MUNAKATA-EPC/Artemis_2025/Common_Data/artemis_pic/artemis_text_colored_white_shined.png

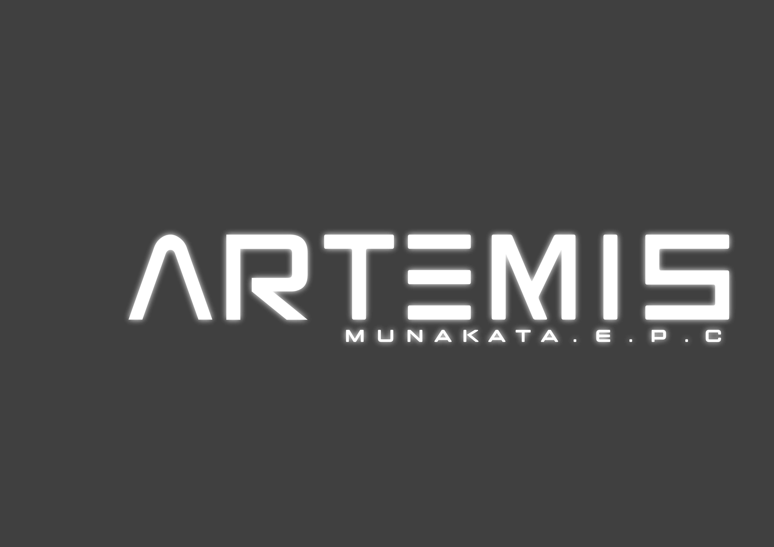
Common_Data/artemis_pic/artemis_text_colored_white_shined.png
