MUNAKATA-EPC/Artemis_2025/Common_Data/artemis_pic/artemis_white.png

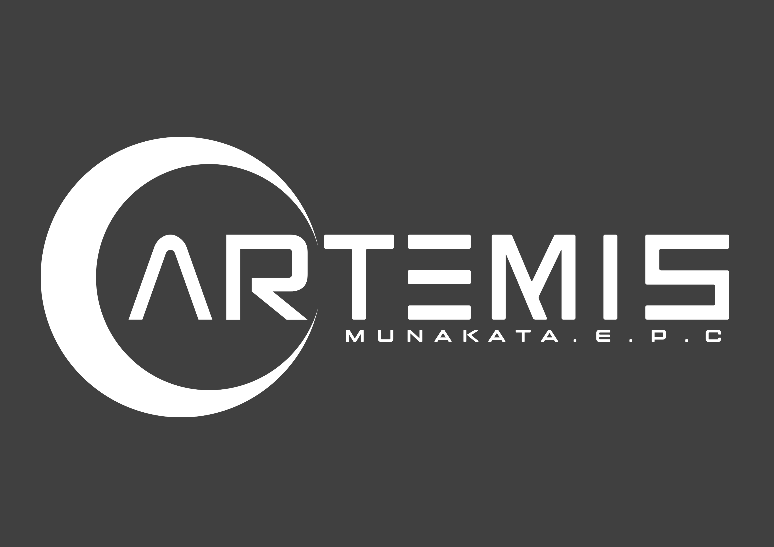
Common_Data/artemis_pic/artemis_white.png
