MUNAKATA-EPC/Artemis_2025/Project_Tsukuyomi (JapanOpen)/Hardware/STEP/VoltageBooster.step

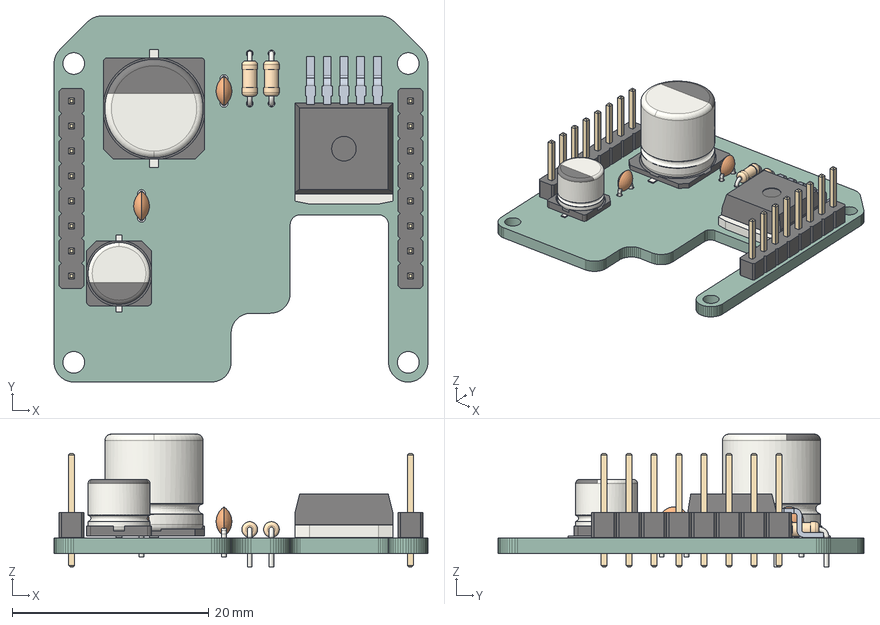
[picture p53: CAD file, 2025-01-11]
Project_Tsukuyomi (JapanOpen)/Hardware/STEP/VoltageBooster.step
38.0 x 37.2 x 13.5 mm
CP_Elec_63x59
R_Axial_DIN0204_L36mm_D16mm_P508mm_Horizontal x 2
CP_Elec_10x105
CQ assembly
PinHeader_1x08_P254mm_Vertical x 2
C_Disc_D30mm_W16mm_P250mm x 2
VoltageBooster PCB
