MUNAKATA-EPC/Artemis_2025/Project_Tsukuyomi (JapanOpen)/Hardware/JLCPCB/Printer/rim.stl

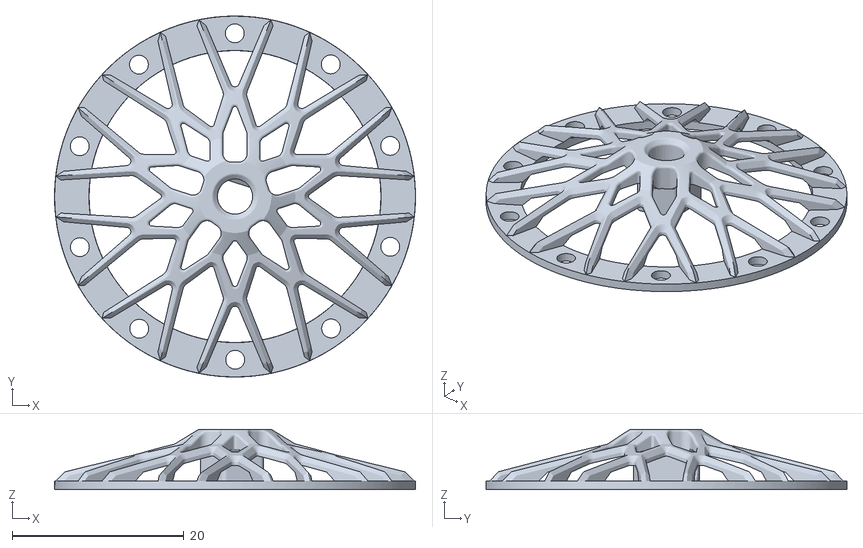
[picture p54: CAD file, 2025-01-11]
Project_Tsukuyomi (JapanOpen)/Hardware/JLCPCB/Printer/rim.stl
42.0 x 42.0 x 7.00
