MUNAKATA-EPC/Artemis_2025/Project_Tsukuyomi (JapanOpen)/Hardware/JLCPCB/Printer/motormount2-1.stl

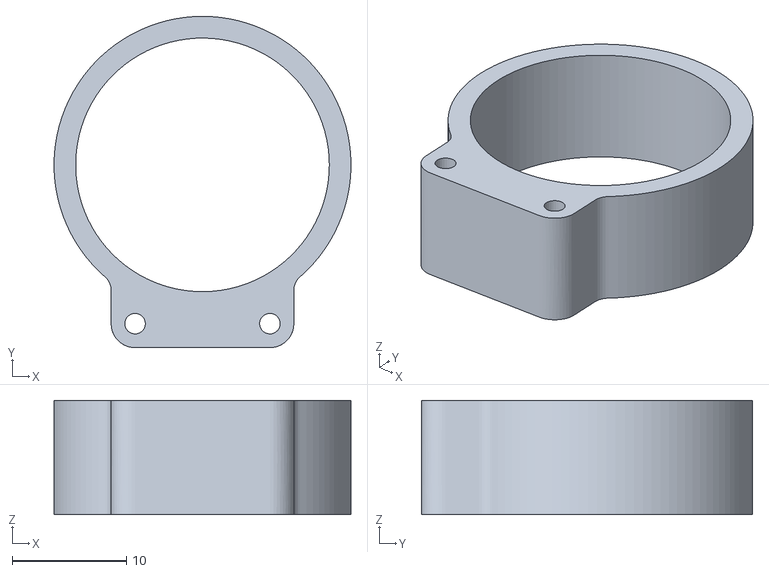
[picture p55: CAD file, 2025-01-11]
Project_Tsukuyomi (JapanOpen)/Hardware/JLCPCB/Printer/motormount2-1.stl
26.0 x 29.0 x 10.0
