MUNAKATA-EPC/Artemis_2025/Project_Tsukuyomi (JapanOpen)/Hardware/JLCPCB/Printer/handle.stl

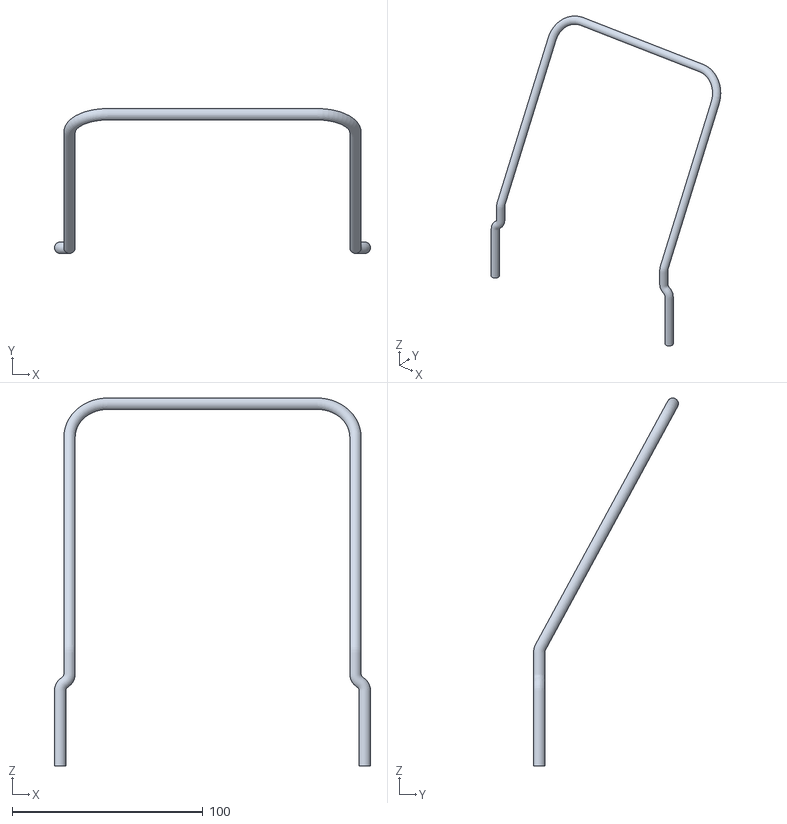
[picture p56: CAD file, 2025-01-11]
Project_Tsukuyomi (JapanOpen)/Hardware/JLCPCB/Printer/handle.stl
165.8 x 76.0 x 193.0
