MUNAKATA-EPC/Artemis_2025/Common_Data/Tournaments_Data/2025_02_JapanOpen/PresentationSheet/SWO008_Munako Artemis_九州.pdf

## 福岡県立宗像高等学校

# チームメンバー

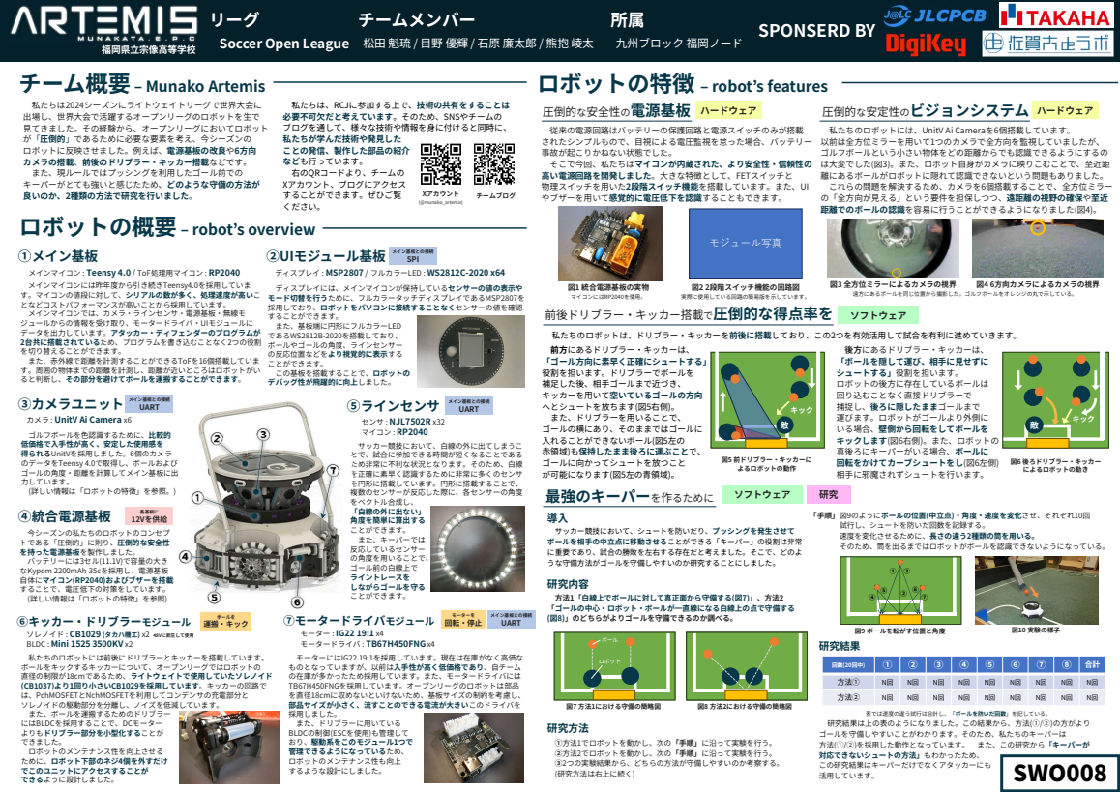
[picture p57: page 1]
研究結果; 九州ブロック 福岡ノード; 前後ドリブラー・キッカー搭載で圧倒的な得点率を; (図8)」のどちらがよりゴールを守備できるのか調べる。; チーム概要‒ Munako Artemis; ロボットの特徴 ‒ robot’s features; 低価格で入手性が高く、安定した使用感を 得られるUnitVを採用しました。6個のカメラ のデータをTeensy 4.0で取得し、ボールおよび ゴールの角度・距離を計算してメイン基板に出 力しています。; UART; 図3 全方位ミラーによるカメラの視界; 図4 6方向カメラによるカメラの視界; 遠方にあるボールを同じ位置から撮影した。ゴルフボールをオレンジの丸で示している。; ➃統合電源基板; 各基板に 12Vを供給; ソフトウェア; ➅キッカー・ドリブラーモジュール; ボールを; 運搬・キック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

SPONSERD BY リーグ
Soccer Open League

松田 魁琉 / 目野 優輝 / 石原 廉太郎 / 熊抱 崚太

私たちは2024シーズンにライトウェイトリーグで世界大会に
出場し、世界大会で活躍するオープンリーグのロボットを生で
見てきました。その経験から、オープンリーグにおいてロボット
が「圧倒的」であるために必要な要素を考え、今シーズンの
ロボットに反映させました。例えば、電源基板の改良や6方向
カメラの搭載、前後のドリブラー・キッカー搭載などです。
また、現ルールではプッシングを利用したゴール前での
キーパーがとても強いと感じたため、どのような守備の方法が
良いのか、2種類の方法で研究を行いました。
ロボットの概要 ‒ robot’s overview
➀メイン基板

ハードウェア 私たちは、RCJに参加する上で、技術の共有をすることは
必要不可欠だと考えています。そのため、SNSやチームの
ブログを通して、様々な技術や情報を身に付けると同時に、
私たちが学んだ技術や発見した
ことの発信、製作した部品の紹介
なども行っています。
右のQRコードより、チームの
Xアカウント、ブログにアクセス
することができます。ぜひご覧
ください。

従来の電源回路はバッテリーの保護回路と電源スイッチのみが搭載
されたシンプルもので、目視による電圧監視を怠った場合、バッテリー
事故が起こりかねない状態でした。
そこで今回、私たちはマイコンが内蔵された、より安全性・信頼性の
高い電源回路を開発しました。大きな特徴として、FETスイッチと
物理スイッチを用いた2段階スイッチ機能を搭載しています。また、UI
やブザーを用いて感覚的に電圧低下を認識することもできます。

私たちのロボットには、UnitV Ai Cameraを6個搭載しています。
以前は全方位ミラーを用いて1つのカメラで全方向を監視していましたが、
ゴルフボールという小さい物体をどの距離からでも認識できるようにするの
は大変でした(図3)。また、ロボット自身がカメラに映りこむことで、至近距
離にあるボールがロボットに隠れて認識できないという問題もありました。
これらの問題を解決するため、カメラを6個搭載することで、全方位ミラー
の「全方向が見える」という要件を担保しつつ、遠距離の視野の確保や至近
距離でのボールの認識を容易に行うことができるようになりました(図4)。

➁UIモジュール基板 メイン基板との接続
SPI ディスプレイ : MSP2807 / フルカラーLED : WS2812C-2020 x64

メインマイコン : Teensy 4.0 / ToF処理用マイコン : RP2040
メインマイコンには昨年度から引き続きTeensy4.0を採用していま
す。マイコンの値段に対して、シリアルの数が多く、処理速度が高いこ
となどコストパフォーマンスが高いことから採用しています。
メインマイコンでは、カメラ・ラインセンサ・電源基板・無線モ
ジュールからの情報を受け取り、モータードライバ・UIモジュールに
データを出力しています。アタッカー・ディフェンダーのプログラムが
2台共に搭載されているため、プログラムを書き込むことなく2つの役割
を切り替えることができます。
また、赤外線で距離を計測することができるToFを16個搭載していま
す。周囲の物体までの距離を計測し、距離が近いところはロボットがい
ると判断し、その部分を避けてボールを運搬することができます。
➂カメラユニット
(詳しい情報は「ロボットの特徴」を参照。) メイン基板との接続
カメラ : UnitV Ai Camera x6 ゴルフボールを色認識するために、比較的

私たちのロボットは、ドリブラー・キッカーを前後に搭載しており、この2つを有効活用して試合を有利に進めていきます。
前方にあるドリブラー・キッカーは、
「ゴール方向に素早く正確にシュートする」
役割を担います。ドリブラーでボールを
補足した後、相手ゴールまで近づき、
キッカーを用いて空いているゴールの方向
へとシュートを放ちます(図5右側)。
また、ドリブラーを用いることで、
ゴールの横にあり、そのままではゴールに
入れることができないボール(図5左の
赤領域)も保持したまま後ろに運ぶことで、
ゴールに向かってシュートを放つこと
が可能になります(図5左の青領域)。
最強のキーパーを作るために
サッカー競技において、シュートを防いだり、プッシングを発生させて
ボールを相手の中立点に移動させることができる「キーパー」の役割は非常
に重要であり、試合の勝敗を左右する存在だと考えました。そこで、どのよ
うな守備方法がゴールを守備しやすいのか研究することにしました。
研究内容
方法1「白線上でボールに対して真正面から守備する(図7)」、方法2 「ゴールの中心・ロボット・ボールが一直線になる白線上の点で守備する

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

➄ラインセンサ メイン基板との接続
UART センサ : NJL7502R x32 マイコン : RP2040

「手順」図9のようにボールの位置(中立点)・角度・速度を変化させ、それぞれ10回
試行し、シュートを防いだ回数を記録する。
速度を変化させるために、⾧さの違う2種類の筒を用いる。
そのため、筒を出るまではロボットがボールを認識できないようになっている。

今シーズンの私たちのロボットのコンセプ
トである「圧倒的」に則り、圧倒的な安全性
を持った電源基板を製作しました。
バッテリーには3セル(11.1V)で容量の大き
なKypom 2200mAh 35cを採用し、電源基板
自体にマイコン(RP2040)およびブザーを搭載
することで、電圧低下の対策をしています。
(詳しい情報は「ロボットの特徴」を参照)

UART モーター : IG22 19:1 x4 モータードライバ : TB67H450FNG x4 モーターにはIG22 19:1を採用しています。現在は在庫がなく高価な

ソレノイド : CB1029 (タカハ機工) x2 48Vに昇圧して使用
BLDC : Mini 1525 3500KV x2 私たちのロボットには前後にドリブラーとキッカーを搭載しています。

ものとなっていますが、以前は入手性が高く低価格であり、自チーム
の在庫が多かったため採用しています。また、モータードライバには
TB67H450FNGを採用しています。オープンリーグのロボットは部品
を直径18cmに収めないといけないため、基板サイズの制約を考慮し、
部品サイズが小さく、流すことのできる電流が大きいこのドライバを
採用しました。
また、ドリブラーに用いている
BLDCの制御(ESCを使用)も管理して
おり、駆動系をこのモジュール1つで
管理できるようになっているため、
ロボットのメンテナンス性も向上
するような設計にしました。

方法➀ | N回 | N回 | N回 | N回 | N回 | N回 | N回 | N回 | N回
方法➁ | N回 | N回 | N回 | N回 | N回 | N回 | N回 | N回 | N回

研究方法
➀方法1でロボットを動かし、次の「手順」に沿って実験を行う。
➁方法2でロボットを動かし、次の「手順」に沿って実験を行う。
➂2つの実験結果から、どちらの方法が守備しやすいのか考察する。
(研究方法は右上に続く)

研究結果は上の表のようになりました。この結果から、方法(➀/➁)の方がより
ゴールを守備しやすいことがわかります。そのため、私たちのキーパーは
方法(➀/➁)を採用した動作となっています。 また、この研究から「キーパーが
対応できないシュートの方法」もわかったため、
この研究結果はキーパーだけでなくアタッカーにも
活用しています。

表では速度の違う試行は合計し、「ボールを防いだ回数」を記している。
