MUNAKATA-EPC/Artemis_2025/Common_Data/component_test/DRV8332DKD/KiCad_Data/DRV8332_test/DRV8332_test.kicad_sch

## KiCad design Common_Data/component_test/DRV8332DKD/KiCad_Data/DRV8332_test/DRV8332_test.kicad_sch (2024-06-09)

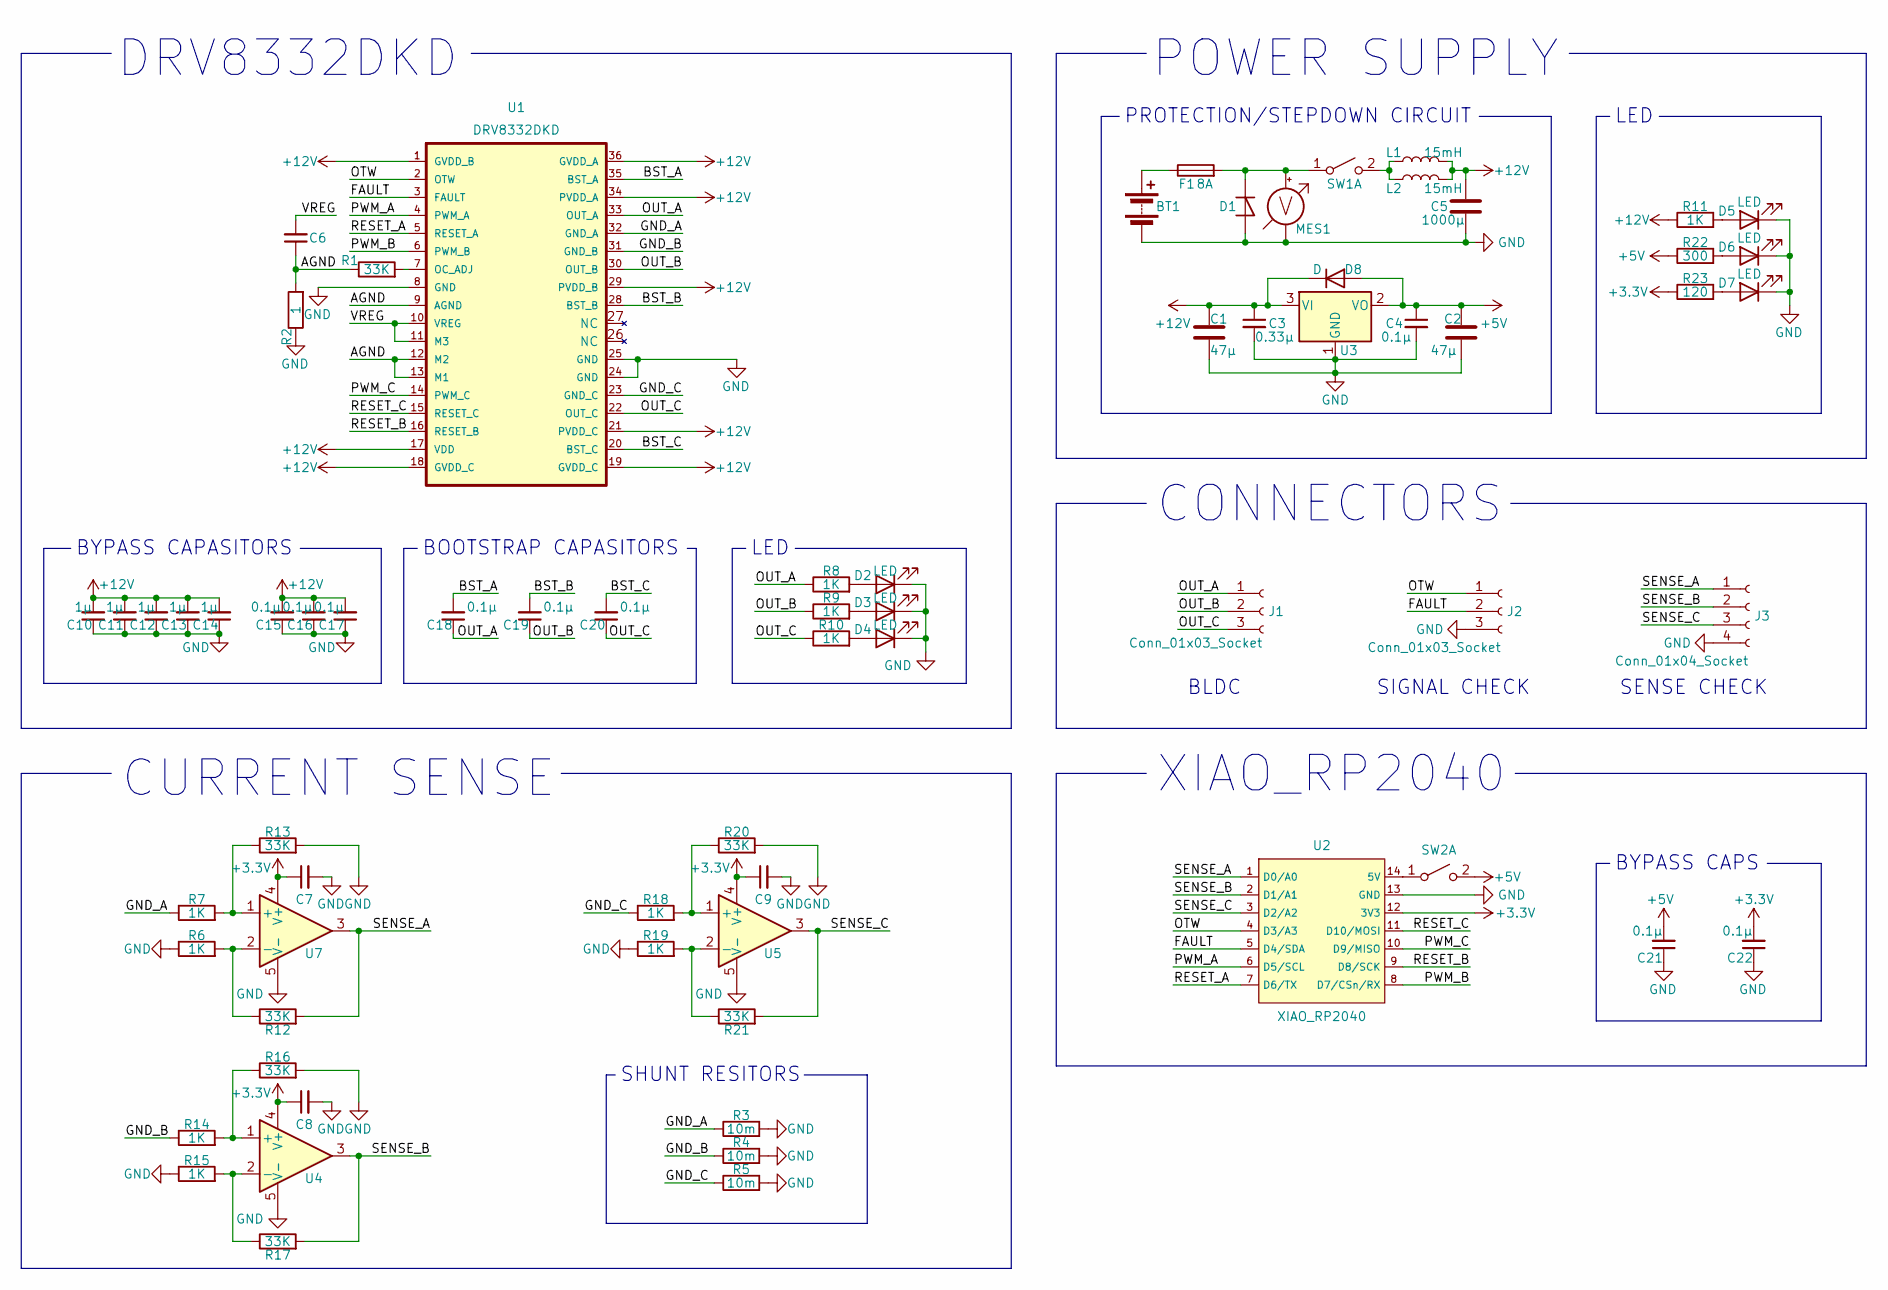
[picture p77: schematic DRV8332_test.kicad_sch]

Parts:
BT1: 11.1v 1300mAh
C1, C2: 47μ
C3: 0.33μ
C4, C15, C16, C17, C18, C19, C20, C21, C22: 0.1μ
C5: 1000μ
C6, C7, C8, C9: C_Small
C10, C11, C12, C13, C14: 1μ
D1: D_Shockley
D2, D3, D4, D5, D6, D7: LED
D8: D
F1: 8A
J1, J2: Conn_01x03_Socket
J3: Conn_01x04_Socket
L1, L2: 15mH
MES1: Voltmeter_DC
R1, R12, R13, R16, R17, R20, R21: 33K
R2: 1
R3, R4, R5: 10m
R6, R7, R8, R9, R10, R11, R14, R15, R18, R19: 1K
R22: 300
R23: 120
SW1, SW2: SW_DPST_x2
U1: DRV8332DKD; SOP65P1420X360-36N
U2: XIAO_RP2040
U3: AZ1117-3.3
U4, U5, U7: type="X" model="OPAMP" lib=""

Connections:
+3.3V: C7.1, C8.1, C9.1, C22.2, R23.1, U2.12 (3V3), U4.4 (V+), U5.4 (V+), U7.4 (V+)
+5V: C2.1, C4.1, C21.2, D8.2 (A), R22.1, SW2.2 (B), U3.2 (VO)
+12V: C1.1, C3.1, C5.1, C10.2, C11.2, C12.2, C13.2, C14.2, C15.2, C16.2, C17.2, D8.1 (K), L1.2, L2.2, R11.1, U1.1 (GVDD_B), U1.17 (VDD), U1.18 (GVDD_C), U1.19 (GVDD_C), U1.21 (PVDD_C), U1.29 (PVDD_B), U1.34 (PVDD_A), U1.36 (GVDD_A), U3.3 (VI)
AGND: C6.1, R1.1, R2.2, U1.9 (AGND), U1.12 (M2), U1.13 (M1)
BST_A: C18.2, U1.35 (BST_A)
BST_B: C19.2, U1.28 (BST_B)
BST_C: C20.2, U1.20 (BST_C)
FAULT: J2.2, U1.3 (FAULT), U2.5 (D4/SDA)
GND: BT1.2 (-), C1.2, C2.2, C3.2, C4.2, C5.2, C7.2, C8.2, C9.2, C10.1, C11.1, C12.1, C13.1, C14.1, C15.1, C16.1, C17.1, C21.1, C22.1, D1.2 (A), D2.1 (K), D3.1 (K), D4.1 (K), D5.1 (K), D6.1 (K), D7.1 (K), J2.3, J3.4, MES1.1 (-), R2.1, R3.2, R4.2, R5.2, R6.1, R13.2, R15.1, R16.2, R19.1, R20.2, U1.8 (GND), U1.24 (GND), U1.25 (GND), U2.13 (GND), U3.1 (GND), U4.5 (V-), U5.5 (V-), U7.5 (V-)
GND_A: R3.1, R7.1, U1.32 (GND_A)
GND_B: R4.1, R14.1, U1.31 (GND_B)
GND_C: R5.1, R18.1, U1.23 (GND_C)
unnamed: BT1.1 (+), F1.1
unnamed: D1.1 (K), F1.2, MES1.2 (+), SW1.1 (A)
unnamed: D2.2 (A), R8.2
unnamed: D3.2 (A), R9.2
unnamed: D4.2 (A), R10.2
unnamed: D5.2 (A), R11.2
unnamed: D6.2 (A), R22.2
unnamed: D7.2 (A), R23.2
unnamed: L1.1, L2.1, SW1.2 (B)
unnamed: R1.2, U1.7 (OC_ADJ)
unnamed: R6.2, R12.1, U7.2 (-)
unnamed: R7.2, R13.1, U7.1 (+)
unnamed: R14.2, R16.1, U4.1 (+)
unnamed: R15.2, R17.1, U4.2 (-)
unnamed: R18.2, R20.1, U5.1 (+)
unnamed: R19.2, R21.1, U5.2 (-)
unnamed: SW2.1 (A), U2.14 (5V)
OTW: J2.1, U1.2 (OTW), U2.4 (D3/A3)
OUT_A: C18.1, J1.1, R8.1, U1.33 (OUT_A)
OUT_B: C19.1, J1.2, R9.1, U1.30 (OUT_B)
OUT_C: C20.1, J1.3, R10.1, U1.22 (OUT_C)
PWM_A: U1.4 (PWM_A), U2.6 (D5/SCL)
PWM_B: U1.6 (PWM_B), U2.8 (D7/CSn/RX)
PWM_C: U1.14 (PWM_C), U2.10 (D9/MISO)
RESET_A: U1.5 (RESET_A), U2.7 (D6/TX)
RESET_B: U1.16 (RESET_B), U2.9 (D8/SCK)
RESET_C: U1.15 (RESET_C), U2.11 (D10/MOSI)
SENSE_A: J3.1, R12.2, U2.1 (D0/A0), U7.3
SENSE_B: J3.2, R17.2, U2.2 (D1/A1), U4.3
SENSE_C: J3.3, R21.2, U2.3 (D2/A2), U5.3
VREG: C6.2, U1.10 (VREG), U1.11 (M3)

Notes on the sheet:
CONNECTORS
BOOTSTRAP CAPASITORS
DRV8332DKD
PROTECTION/STEPDOWN CIRCUIT
POWER SUPPLY
BYPASS CAPASITORS
SENSE CHECK
BYPASS CAPS
LED
XIAO_RP2040
BLDC
SHUNT RESITORS
CURRENT SENSE
SIGNAL CHECK
