MUNAKATA-EPC/Artemis_2025/Common_Data/component_test/RP2040/KiCad_Data/RP2040_test/RP2040_test.kicad_sch

## KiCad design Common_Data/component_test/RP2040/KiCad_Data/RP2040_test/RP2040_test.kicad_sch (2024-06-09)

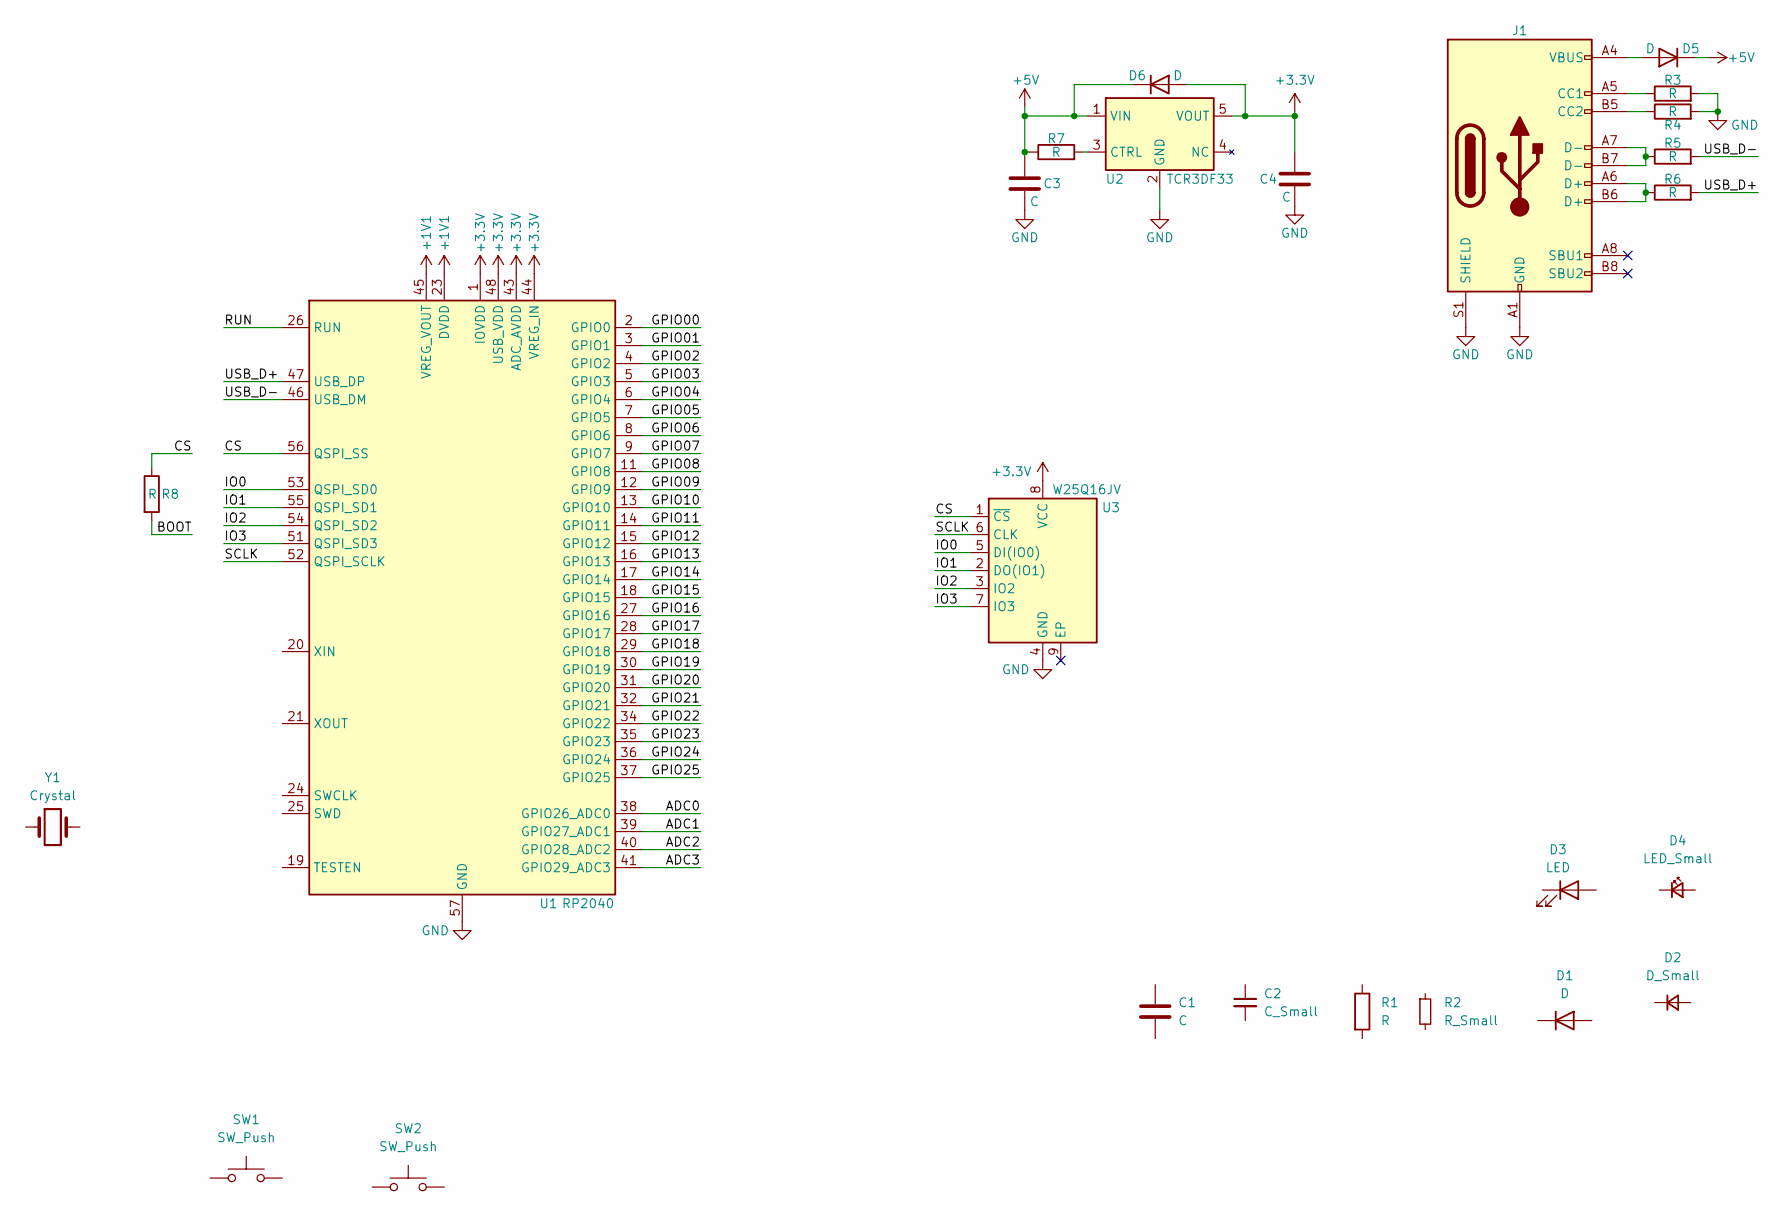
[picture p78: schematic RP2040_test.kicad_sch]

Parts:
C1, C3, C4: C
C2: C_Small
D1, D5, D6: D
D2: D_Small
D3: LED
D4: LED_Small
J1: USB_C_Receptacle_USB2.0
R1, R3, R4, R5, R6, R7, R8: R
R2: R_Small
SW1, SW2: SW_Push
U1: RP2040; QFN-56-1EP_7x7mm_P0.4mm_EP3.2x3.2mm
U2: TCR3DF33; SOT-553
U3: W25Q16JV; WSON-8-1EP_6x5mm_P1.27mm_EP3.4x4.3mm
Y1: Crystal

Connections:
+1V1: U1.23 (DVDD), U1.45 (VREG_VOUT), U1.50 (DVDD)
+3.3V: C4.1, D6.2 (A), U1.1 (IOVDD), U1.10 (IOVDD), U1.22 (IOVDD), U1.33 (IOVDD), U1.42 (IOVDD), U1.43 (ADC_AVDD), U1.44 (VREG_IN), U1.48 (USB_VDD), U1.49 (IOVDD), U2.5 (VOUT), U3.8 (VCC)
+5V: C3.1, D5.1 (K), D6.1 (K), R7.1, U2.1 (VIN)
ADC0: U1.38 (GPIO26_ADC0)
ADC1: U1.39 (GPIO27_ADC1)
ADC2: U1.40 (GPIO28_ADC2)
ADC3: U1.41 (GPIO29_ADC3)
BOOT: R8.2
CS: R8.1, U1.56 (QSPI_SS), U3.1 (~CS)
GND: C3.2, C4.2, J1.A1 (GND), J1.A12 (GND), J1.B1 (GND), J1.B12 (GND), J1.S1 (SHIELD), R3.2, R4.2, U1.57 (GND), U2.2 (GND), U3.4 (GND)
GPIO00: U1.2 (GPIO0)
GPIO01: U1.3 (GPIO1)
GPIO02: U1.4 (GPIO2)
GPIO03: U1.5 (GPIO3)
GPIO04: U1.6 (GPIO4)
GPIO05: U1.7 (GPIO5)
GPIO06: U1.8 (GPIO6)
GPIO07: U1.9 (GPIO7)
GPIO08: U1.11 (GPIO8)
GPIO09: U1.12 (GPIO9)
GPIO10: U1.13 (GPIO10)
GPIO11: U1.14 (GPIO11)
GPIO12: U1.15 (GPIO12)
GPIO13: U1.16 (GPIO13)
GPIO14: U1.17 (GPIO14)
GPIO15: U1.18 (GPIO15)
GPIO16: U1.27 (GPIO16)
GPIO17: U1.28 (GPIO17)
GPIO18: U1.29 (GPIO18)
GPIO19: U1.30 (GPIO19)
GPIO20: U1.31 (GPIO20)
GPIO21: U1.32 (GPIO21)
GPIO22: U1.34 (GPIO22)
GPIO23: U1.35 (GPIO23)
GPIO24: U1.36 (GPIO24)
GPIO25: U1.37 (GPIO25)
IO0: U1.53 (QSPI_SD0), U3.5 (DI(IO0))
IO1: U1.55 (QSPI_SD1), U3.2 (DO(IO1))
IO2: U1.54 (QSPI_SD2), U3.3 (IO2)
IO3: U1.51 (QSPI_SD3), U3.7 (IO3)
unnamed: D5.2 (A), J1.A4 (VBUS), J1.A9 (VBUS), J1.B4 (VBUS), J1.B9 (VBUS)
unnamed: J1.A5 (CC1), R3.1
unnamed: J1.A6 (D+), J1.B6 (D+), R6.1
unnamed: J1.A7 (D-), J1.B7 (D-), R5.1
unnamed: J1.B5 (CC2), R4.1
unnamed: R7.2, U2.3 (CTRL)
RUN: U1.26 (RUN)
SCLK: U1.52 (QSPI_SCLK), U3.6 (CLK)
USB_D+: R6.2, U1.47 (USB_DP)
USB_D-: R5.2, U1.46 (USB_DM)
