MUNAKATA-EPC/Artemis_2025/Project_Tsukuyomi (JapanOpen)/Software/main_teensy40/src/main.cpp

//                                                                                                 ,,
//   MMP""MM""YMM                     `7MM                                                           db
//   P'   MM   `7                       MM
//        MM      ,pP"Ybd `7MM  `7MM    MM  ,MP'`7MM  `7MM  `7M'   `MF' ,pW"Wq.  `7MMpMMMb.pMMMb.  `7MM
//        MM      8I   `"   MM    MM    MM ;Y     MM    MM    VA   ,V  6W'   `Wb   MM    MM    MM    MM
//        MM      `YMMMa.   MM    MM    MM;Mm     MM    MM     VA ,V   8M     M8   MM    MM    MM    MM
//        MM      L.   I8   MM    MM    MM `Mb.   MM    MM      VVV    YA.   ,A9   MM    MM    MM    MM
//      .JMML.    M9mmmP'   `Mbod"YML..JMML. YA.  `Mbod"YML.    ,V      `Ybmd9'  .JMML  JMML  JMML..JMML.
//                                                           ,V
//                                                        OOb"

// Tsukuyomi Main Program For JapanOpen-2025

// Please check out the history of updates : https://github.com/MUNAKATA-EPC/Artemis_2025/commits/main/

#include <Arduino.h>

#include "common/sensors_variables.hpp"
#include "common/serial.hpp"
#include "common/motor.hpp"

#include "modules/kicker.hpp"
#include "modules/BNO055.hpp"
#include "modules/button.hpp"

#include "process/engelline.hpp"
#include "process/attacker.hpp"
#include "process/defender.hpp"
#include "process/ball_process.hpp"

#include "ui/ui.hpp"

BNO055 bno055;
Kicker f_kicker;
Kicker b_kicker;

Timer test;

Button debug_bt;
Button start_bt;

void play_startup_sound()
{
    tone(2, 3500, 90);
    delay(110);
    tone(2, 3500, 90);
    delay(440);
    tone(2, 2700, 90);
    delay(110);
    tone(2, 3500, 90);
    delay(110);
    tone(2, 4500, 90);
    delay(110);
}
void play_startup_sound_pre()
{
    tone(2, 3500, 90);
    delay(110);
    tone(2, 3500, 90);
    delay(110);
    tone(2, 3500, 90);
    delay(110);
}

void setup() {
    Serial.println(9600);

    play_startup_sound_pre();

    init_motor();
    init_serial();
    init_ball_process();

    bno055.init(6);
    debug_bt.init(6, Button::Button_Value_Type::PULLDOWN);
    start_bt.init(5, Button::Button_Value_Type::PULLDOWN);
    
    f_kicker.init(30, 31);
    b_kicker.init(30, 32);

    init_engelline();
    init_ui();

    play_startup_sound();
}

void loop() {
    process_serial();
    process_engelline(is_running);
    process_ball_process();

    bno055.process();
    gyro_deg = bno055.get_degrees();

    f_kicker.loop();
    b_kicker.loop();

    debug_bt.loop();
    start_bt.loop();

    //メインルーチンの実行
    if(start_bt.is_pushed())
    {
        is_running = !is_running;
    }

    if(debug_bt.is_pushed())
    {
        f_kicker.kick(100);
        b_kicker.kick(100);
        is_running = !is_running;
        process_mode = 0;
    }

    if(is_running)
    {
        if(process_mode == 0)       //黄色ゴール・アタッカー
        {
            process_attacker(true, 100);
        }
        else if(process_mode == 1)  //青色ゴール・アタッカー
        {
            process_attacker(false, 100);
        }
        else if(process_mode == 2)  //黄色ゴール・ディフェンダー
        {
            process_defender(true);
        }
        else if(process_mode == 3)  //青色ゴール・ディフェンダー
        {
            process_defender(false);
        }
    }
    else
    {
        motor_set_bldc(0, 0);
        motor_direct_drive(0, 0, 0, 0);
    }

    process_ui();
}
