MUNAKATA-EPC/Artemis_2025/Project_Tsukuyomi (JapanOpen)/Software/main_teensy40/src/process/engelline.cpp

#include <Arduino.h>
#include <Adafruit_NeoPixel.h>

#include "common/sensors_variables.hpp"
#include "engelline.hpp"

Adafruit_NeoPixel pixels = Adafruit_NeoPixel(32, 3, NEO_GRB + NEO_KHZ800);

double line_sensors_deg[16] = { 22.5 * 0,   22.5 * 1,   22.5 * 2,   22.5 * 3,
  22.5 * 4,   22.5 * 5,   22.5 * 6,   22.5 * 7,
  22.5 * 8,   22.5 * 9,   22.5 * 10,  22.5 * 11,
  22.5 * 12,  22.5 * 13,  22.5 * 14,  22.5 * 15,
  };

int line_deg;
int line_first_deg;
int previous_line_deg;

int line_evacuation_deg;

bool is_halfout;

bool is_exist_deg_value_in_range(int check_value, int base_value, int check_range)
{
    if(base_value - check_range < 0)
    {
        if( check_value <= base_value + check_range || 
            check_value >= base_value - check_range + 360)
        {
            return true;
        }
        else
        {
            return false;
        }
    }
    else if(base_value + check_range > 360)
    {
        if( check_value <= base_value + check_range - 360 ||
            check_value >= base_value - check_range)
        {
            return true;
        }
        else
        {
            return false;
        }
    }
    else
    {
        if( check_value >= base_value - check_range &&
            check_value <= base_value + check_range)
        {
            return true;
        }
        else
        {
            return false;
        } 
    }
}

int get_count_of_detected_sensor()
{
    int ret = 0;

    for(int i = 0; i < 16; i++)
    {
        if(line_data[i] == 1)
        {
            ret++;
        }
    }

    return ret;
}

bool is_line_detected()
{
    bool ret = false;

    for(int i = 0; i < 16; i++)
    {
        if(line_data[i] == 1)
        {
            ret = true;
        }
    }

    return ret;
}

bool is_line_evacuation()
{
    return is_line_detected() || is_halfout;
}

bool is_previous_line_detected()
{
    return previous_line_deg != -1;
}


Timer send_timer_line;
void init_engelline()
{
    pixels.setBrightness(110);
    pixels.begin();  

    for(int i = 0; i < 32; i++)
    {
      /*
      pixels.rainbow(i);
      for(int j = 0; j < 32; j++)
      {
        if(j > i)
        {
            pixels.setPixelColor(j, pixels.Color(0, 0, 0));
        }
      }*/
      //pixels.setPixelColor(i, pixels.Color(30, 245, 80));
      
      pixels.setPixelColor(i, pixels.Color(180, 40, 255));
      pixels.show();

      delay(10);
    }
}

void process_engelline(bool running)
{
    send_timer_line.tick();
    send_timer_line.start();

    if(get_count_of_detected_sensor() > 14)
    {
        return;
    }

    if(send_timer_line.get_value() >= 500)
    {
        if(running)
        {
            //LEDの発光
            pixels.clear();
            
            for(int i = 0; i < 32; i++)
            {
                pixels.setPixelColor(i, pixels.Color(0, 255, 0));       //グリーン
                //pixels.setPixelColor(i, pixels.Color(255, 0, 0));    //パープル
                //pixels.setPixelColor(i, pixels.Color(255, 255, 255));   //ホワイト
                //pixels.setPixelColor(i, pixels.Color(50, 255, 100));    //エメラルドグリーン
            }
            
            pixels.show();
        }
        else
        {
            pixels.clear();
            pixels.show();
        }

        send_timer_line.reset();
    }

    if(is_line_detected())
    {
        //tone(3, 4000, 100);
        
        double line_vec_x = 0, line_vec_y = 0;

        for(int i = 0; i < 16; i++)
        {
            if(line_data[i] == 1)
            {
                line_vec_x += cos(radians(line_sensors_deg[i]));
                line_vec_y += sin(radians(line_sensors_deg[i]));
            }
        }

        //********************************************************ここ処理怪しいかもだから作り直した方がいい
        line_deg = 360 - degrees(atan2(line_vec_y, line_vec_x));

        if(line_deg <= 360)
        {
            line_deg = 360 - line_deg;
        }
        else
        {
            line_deg = 360 - (line_deg - 180) + 180;
        }
    }
    else
    {
        line_deg = -1;
    }

    //今回初めてラインが反応したら
    if( is_line_detected() && !is_previous_line_detected())
    {
        if(!is_halfout)
        {
            line_first_deg = line_deg;
            previous_line_deg = line_deg;
            line_evacuation_deg = line_first_deg;

            return;
        }
    }

    //さっきまでラインが反応していたら
    if( !is_line_detected() && is_previous_line_detected())
    {
        if(!is_halfout)
        {
            line_first_deg = -1;
        }
    }

    //継続してラインが反応していたら
    if( is_line_detected() && is_previous_line_detected())
    {
        //前回とのラインの角度を比較して、もし大きく値がずれていたら「ハーフアウト」判定にする
        if(!is_exist_deg_value_in_range(line_deg, line_first_deg, 130))
        {
            is_halfout = true;
        }
        else
        {
            is_halfout = false;

            //基準角度と大きくずれていなかったら、基準角度を現在の角度に置き換え
            if(is_exist_deg_value_in_range(line_deg, line_first_deg, 80))
            {
                line_first_deg = line_deg;
            }
        }
    }

    previous_line_deg = line_deg;

    line_evacuation_deg = line_first_deg;
}
