MUNAKATA-EPC/Artemis_2025/Project_Tsukuyomi (JapanOpen)/Software/main_teensy40/src/common/serial.cpp

#include <Arduino.h>
#include "serial.hpp"
#include "sensors_variables.hpp"

int gyro_deg;

int ball_deg;
int ball_dis;
int ygoal_deg;
int ygoal_dis;
int bgoal_deg;
int bgoal_dis;

int line_data[16];

void init_serial()
{
    Serial1.begin(115200);
    Serial1.setTimeout(10);

    Serial3.begin(115200);
    Serial3.setTimeout(10);
}

void process_serial()
{
    while(Serial1.available() > 0)
    {
        int temp = Serial1.readStringUntil('a').toInt();
        ball_deg = temp <= 360 ? temp : ball_deg;

        temp = Serial1.readStringUntil('b').toInt();
        ball_dis = temp <= 240 ? temp : ball_dis;

        temp = Serial1.readStringUntil('c').toInt();
        ygoal_deg = temp <= 360 ? temp : ygoal_deg;

        temp = Serial1.readStringUntil('d').toInt();
        ygoal_dis = temp <= 240 ? temp : ygoal_dis;
        
        temp = Serial1.readStringUntil('e').toInt();
        bgoal_deg = temp <= 360 ? temp : bgoal_deg;

        temp = Serial1.readStringUntil('f').toInt();
        bgoal_dis = temp <= 240 ? temp : bgoal_dis;

        ball_deg = ball_deg != -1 ? (ball_deg) % 360 : -1;
    }

    int _line_data = -1;
    
    while(Serial3.available() > 0)
    {
        _line_data = Serial3.readStringUntil('\n').toInt();
        
        if(_line_data > pow(2, 16))
        {
            return;
        }

        for(int i = 15; i >= 0; i--)
        {
            if(_line_data - pow(2, i) >= 0)
            {
                _line_data -= pow(2, i);
                line_data[i] = 1;
            }
            else
            {
                line_data[i] = 0;
            }
        }
    }

    // Serial.print(ball_deg);
    // Serial.print(",");
    // Serial.print(ball_dis);
    // Serial.print(",");
    // Serial.print(ygoal_deg);
    // Serial.print(",");
    // Serial.print(ygoal_dis);
    // Serial.print(",");
    // Serial.print(bgoal_deg);
    // Serial.print(",");
    // Serial.println(bgoal_dis);
      
    if(_line_data != -1)
    {
        // Serial.print(_line_data);
        // Serial.print(",");
        for(int i = 0; i < 16; i++)
        {
            Serial.print(line_data[i]);
        }
        Serial.print("\n");
    }
}
