MUNAKATA-EPC/Artemis_2025/Project_Tsukuyomi (JapanOpen)/Software/main_teensy40/src/modules/BNO055.hpp

#ifndef _BNO055_HPP
#define _BNO055_HPP

#include <Arduino.h>
#include <Wire.h>
#include <Adafruit_BNO055.h>

#include "button.hpp"

class BNO055{
public:
    void init(int reset_pin, int sub_pin = -1);
    void process();
    void reset_degree();
    int get_degrees();

private:
    Adafruit_BNO055 bno = Adafruit_BNO055(55, 0x28, &Wire);
    Button reset;
};

#endif
