MUNAKATA-EPC/Artemis_2025/Project_Tsukuyomi (JapanOpen)/Software/main_teensy40/src/common/vector.hpp

#ifndef _VECTOR_HPP
#define _VECTOR_HPP

#include <Arduino.h>

class Vector{
public:
    Vector(float rad, float size);

    void set(float rad, float size);
    void add(Vector a);
    void sub(Vector a);
    int get_deg();
    float get_size();

    Vector get_x_component();
    Vector get_y_component();

private:
    float _rad;
    float _size;
};

#endif
