MUNAKATA-EPC/Artemis_2025/Project_Tsukuyomi (JapanOpen)/Software/main_teensy40/src/modules/button.hpp

#ifndef _BUTTON_HPP
#define _BUTTON_HPP

class Button{
public:
    typedef enum{
        PULLUP,
        PULLDOWN
    }Button_Value_Type;

    void init(int pin, Button_Value_Type type);
    void loop();
    bool is_pushing();
    bool is_pushed();
    bool is_released();
    bool is_init();
private:
    int _pin;
    int _push_time;
    bool _is_init;
    Button_Value_Type _value_type;
};

#endif
